ericrlau/NumDiscipline/images/proto1.jpg

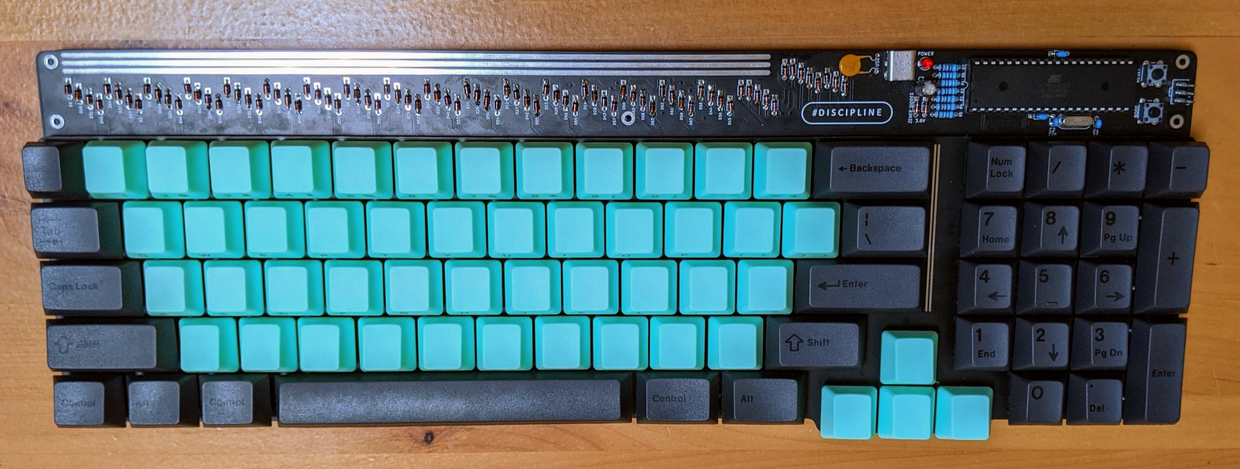
images/proto1.jpg
